345ljh/Artisans_Tome_Release/documentation/2025-09-26-21-44-38.png

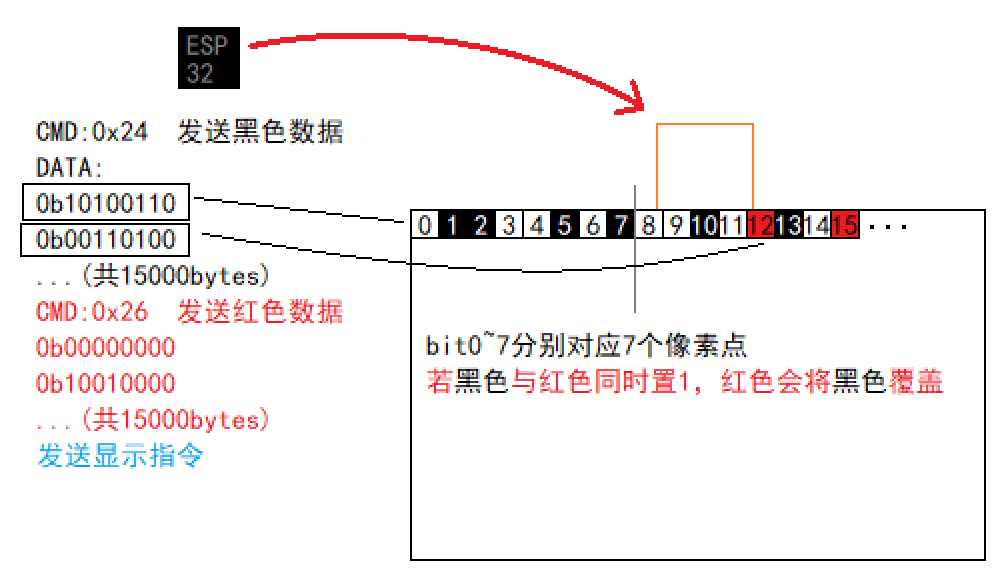
documentation/2025-09-26-21-44-38.png
