345ljh/Artisans_Tome_Release/handbook/0.png

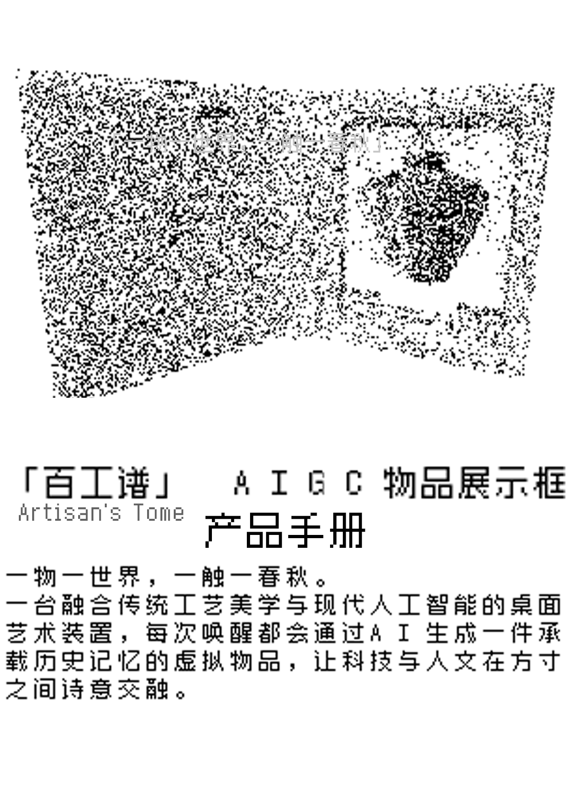
handbook/0.png
