345ljh/Artisans_Tome_Release/handbook/1.png

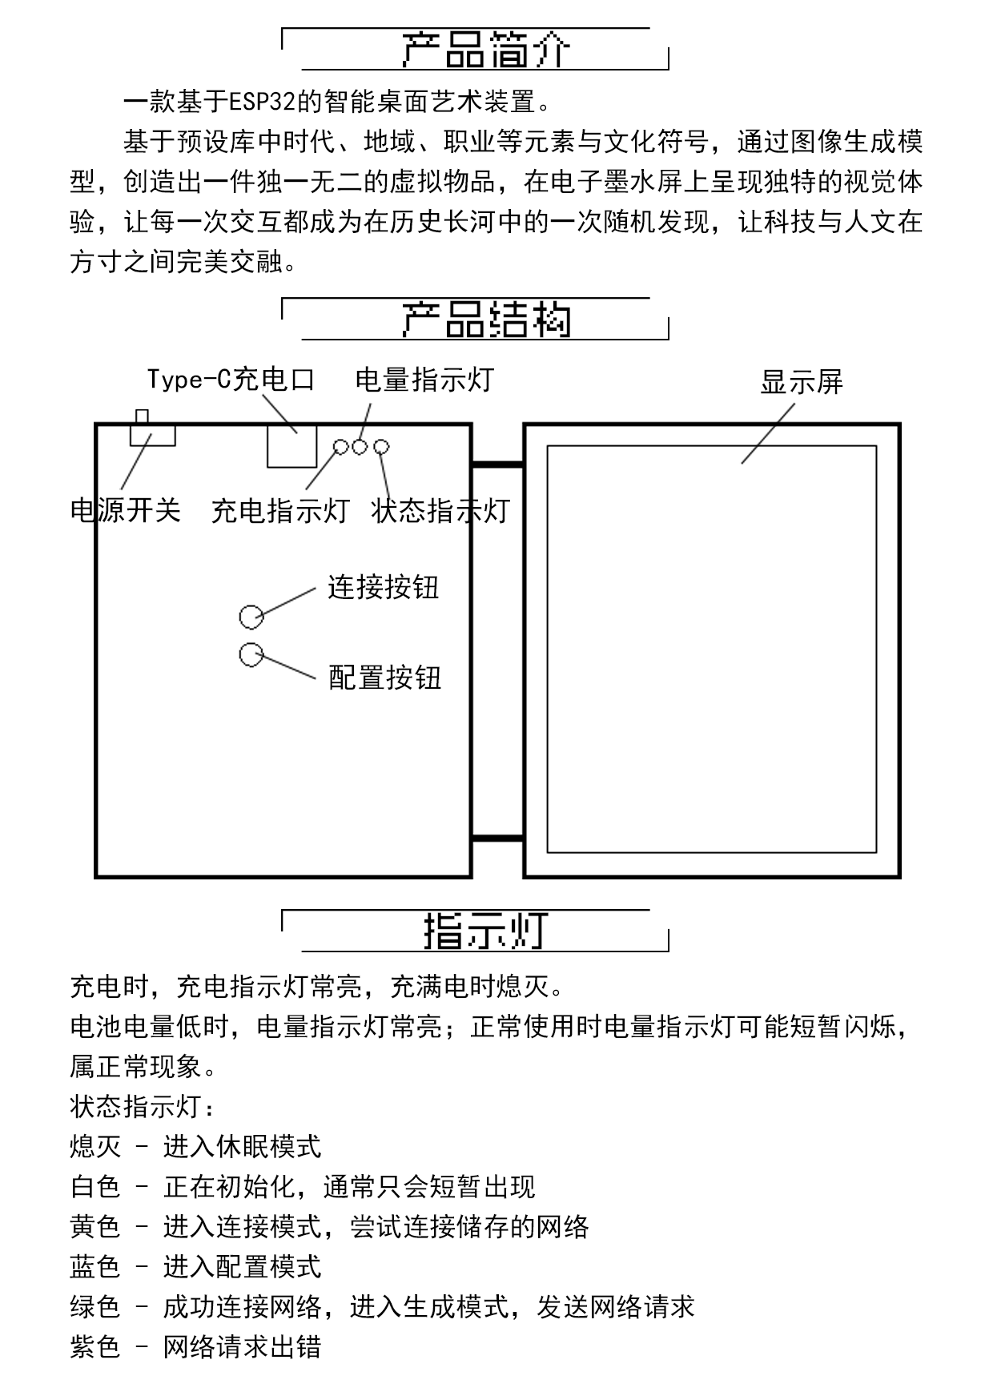
handbook/1.png
