345ljh/Artisans_Tome_Release/handbook/2.png

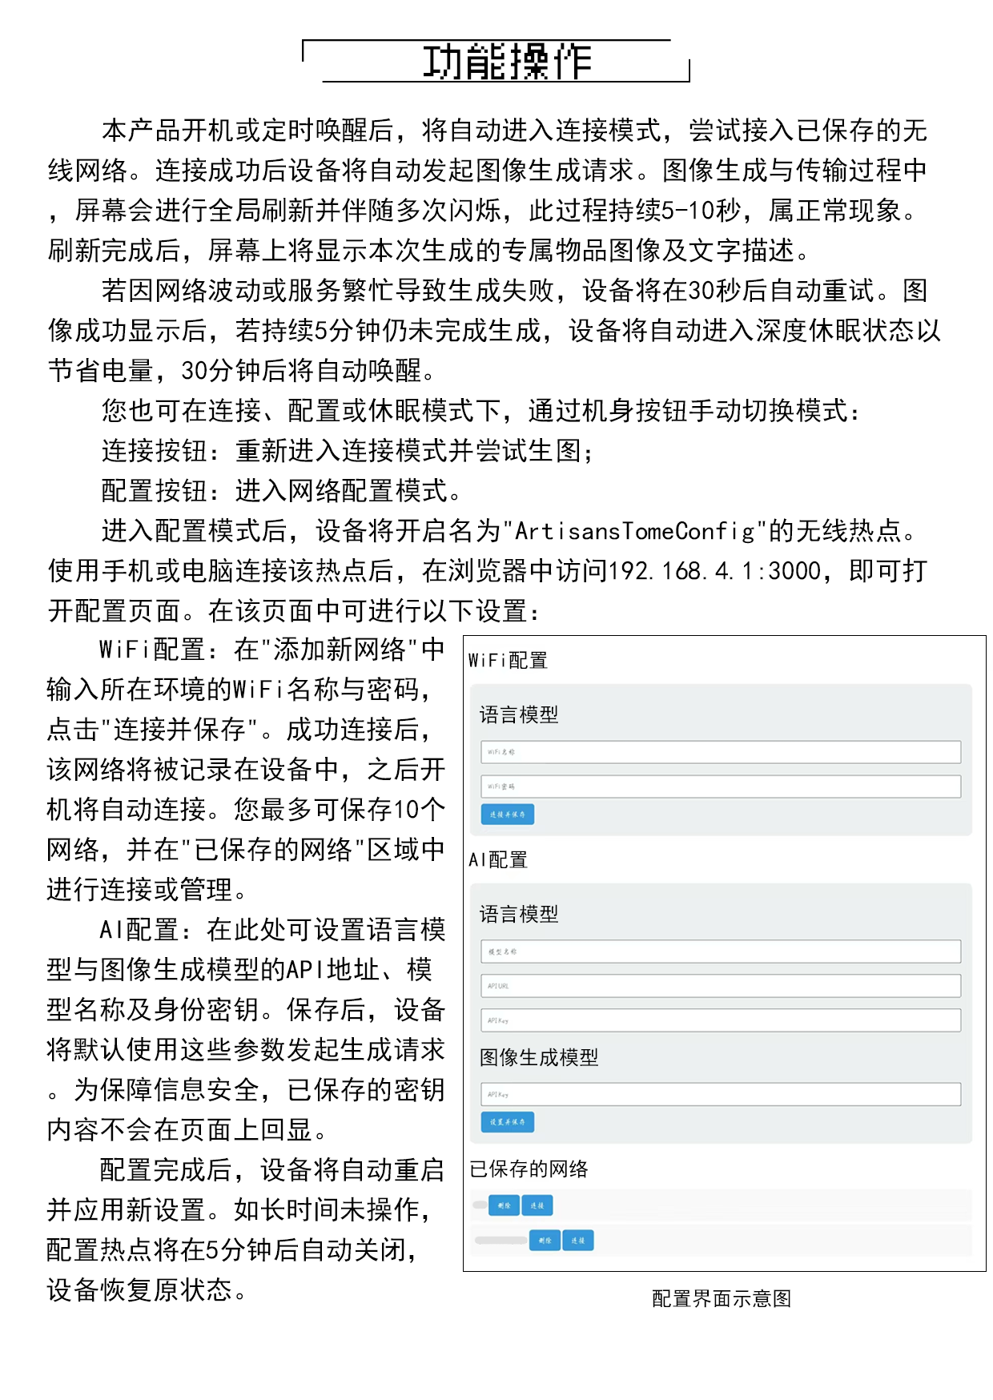
handbook/2.png
