345ljh/Artisans_Tome_Release/handbook/3.png

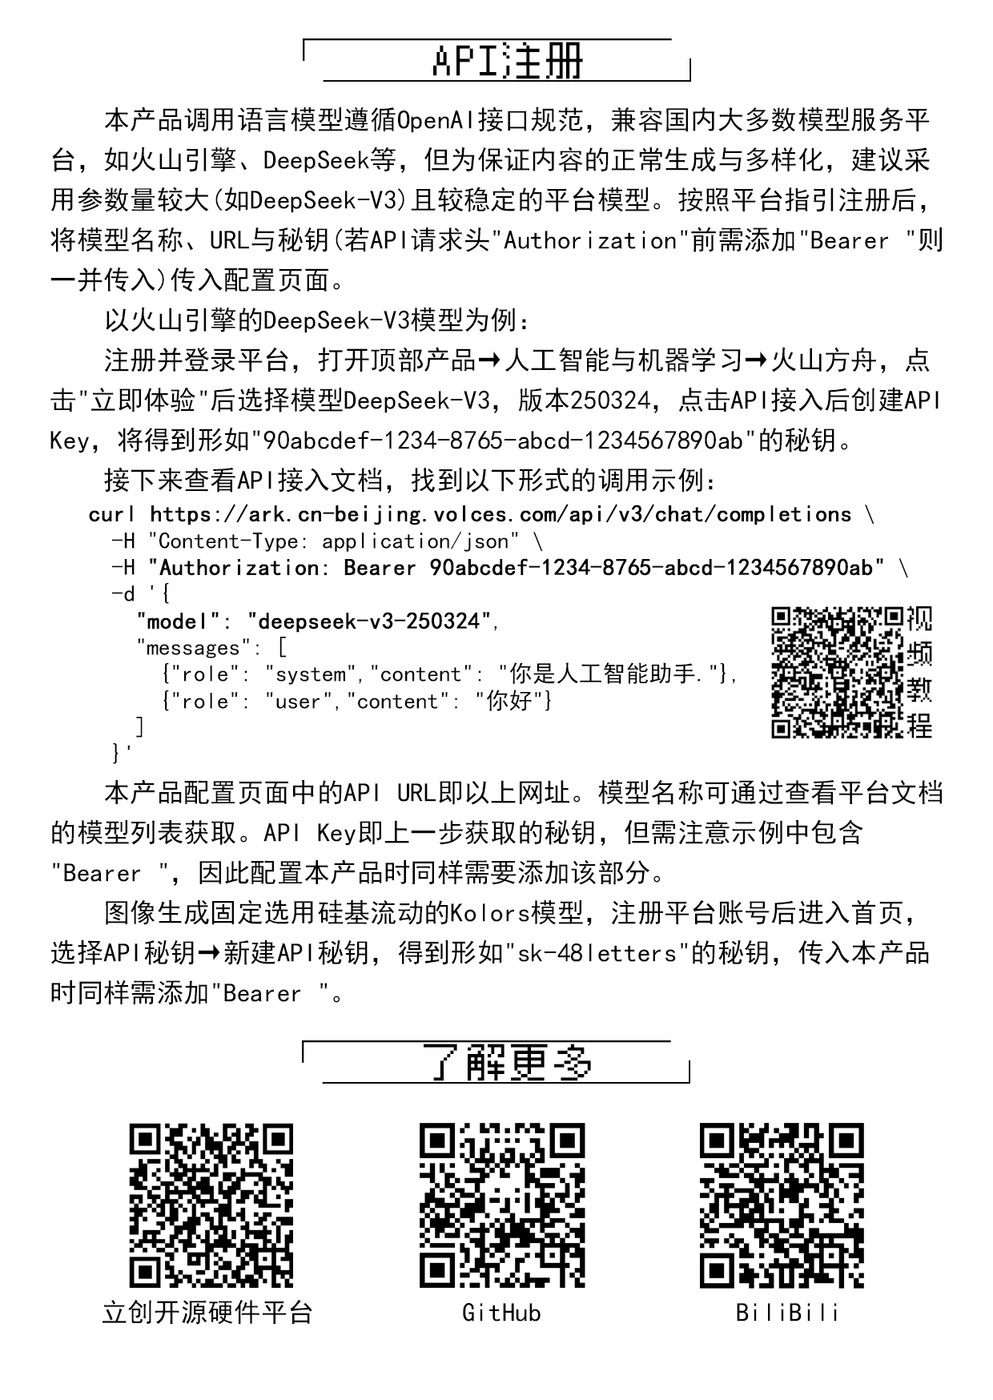
handbook/3.png
